Dennis960/SmartCube/Firmware/PY32/src/setup/py32f0xx_hal_msp.c

/**
  ******************************************************************************
  * @file    py32f0xx_hal_msp.c
  * @author  MCU Application Team
  * @brief   This file provides code for the MSP Initialization
  *          and de-Initialization codes.
  ******************************************************************************
  * @attention
  *
  * <h2><center>&copy; Copyright (c) Puya Semiconductor Co.
  * All rights reserved.</center></h2>
  *
  * <h2><center>&copy; Copyright (c) 2016 STMicroelectronics.
  * All rights reserved.</center></h2>
  *
  * This software component is licensed by ST under BSD 3-Clause license,
  * the "License"; You may not use this file except in compliance with the
  * License. You may obtain a copy of the License at:
  *                        opensource.org/licenses/BSD-3-Clause
  *
  ******************************************************************************
  */

/* Includes ------------------------------------------------------------------*/

/* Private typedef -----------------------------------------------------------*/
/* Private define ------------------------------------------------------------*/
/* Private macro -------------------------------------------------------------*/
/* Private variables ---------------------------------------------------------*/
/* Private function prototypes -----------------------------------------------*/
/* External functions --------------------------------------------------------*/

/**
  * @brief 初始化全局MSP
  */
void HAL_MspInit(void)
{
}

/************************ (C) COPYRIGHT Puya *****END OF FILE******************/
